thatfellarobin/doublemag-fixture/main.py

import sys
from PyQt5.QtWidgets import QApplication

from ui import DoubleMagnetGUI

if __name__ == '__main__':
    app = QApplication(sys.argv)
    window = DoubleMagnetGUI()
    window.show()
    sys.exit(app.exec_())
